ergobrush/ergobrush.github.io/img/anbo1.jpeg

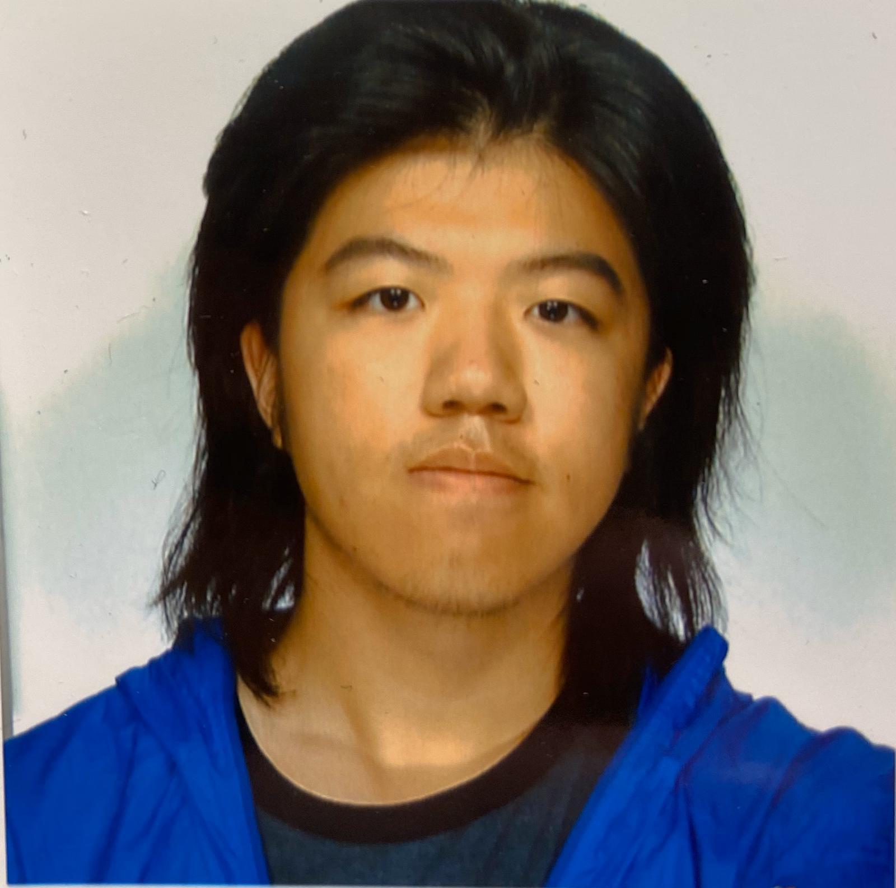
img/anbo1.jpeg
