ergobrush/ergobrush.github.io/img/andre.jpg

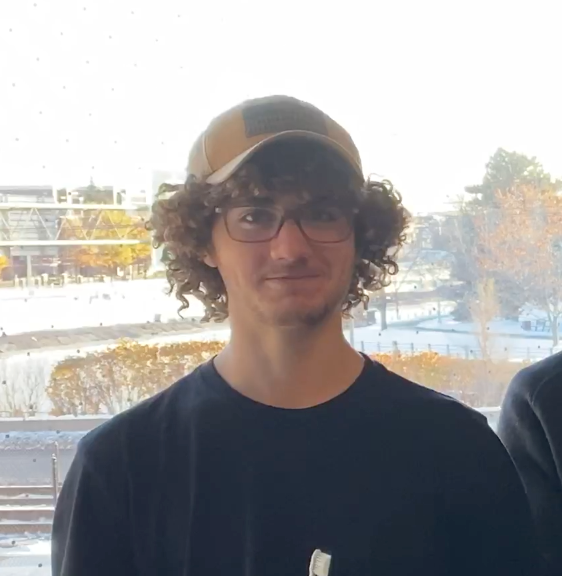
img/andre.jpg
