ergobrush/ergobrush.github.io/img/george.png

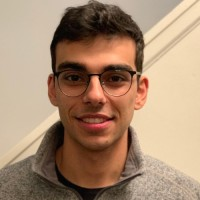
img/george.png
