ergobrush/ergobrush.github.io/img/stem-image.jpg

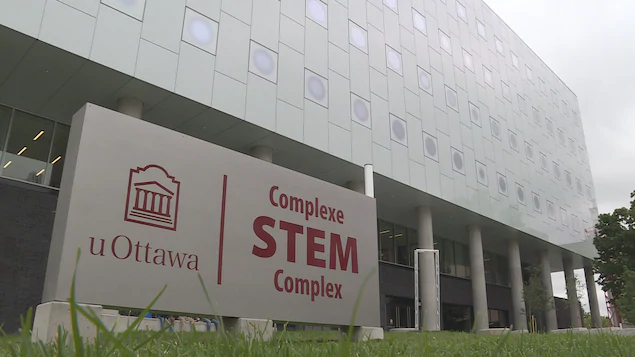
img/stem-image.jpg
