ergobrush/ergobrush.github.io/img/stvincent2.jpg

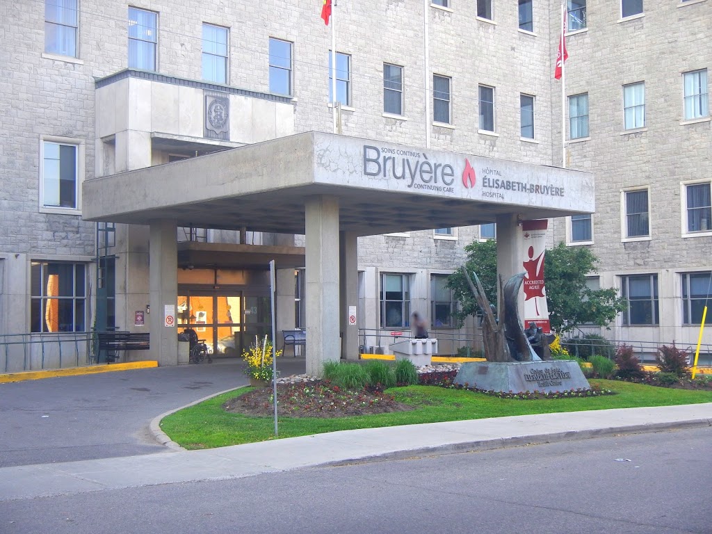
img/stvincent2.jpg
