ergobrush/ergobrush.github.io/img/toothbrush1.jpg

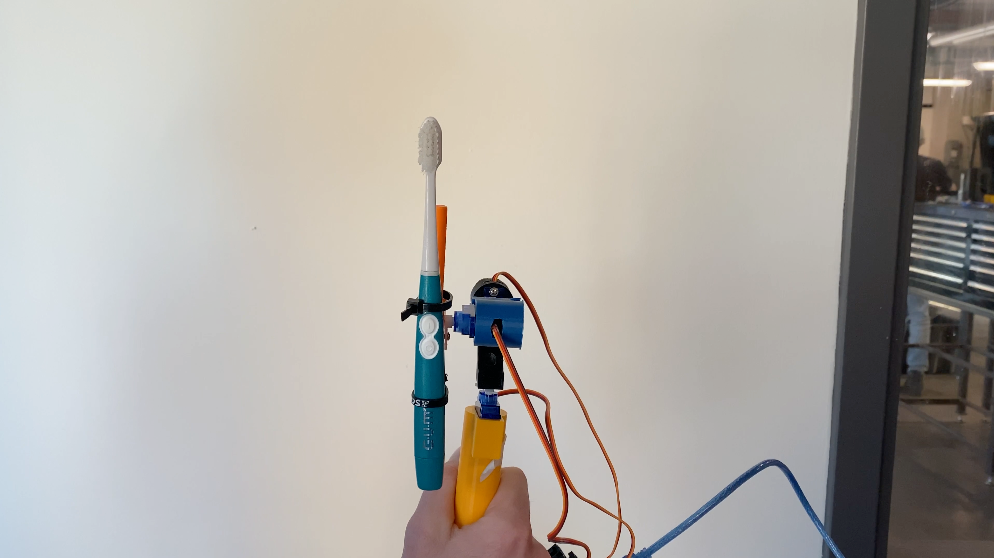
img/toothbrush1.jpg
