ergobrush/ergobrush.github.io/img/toothbrush.jpg

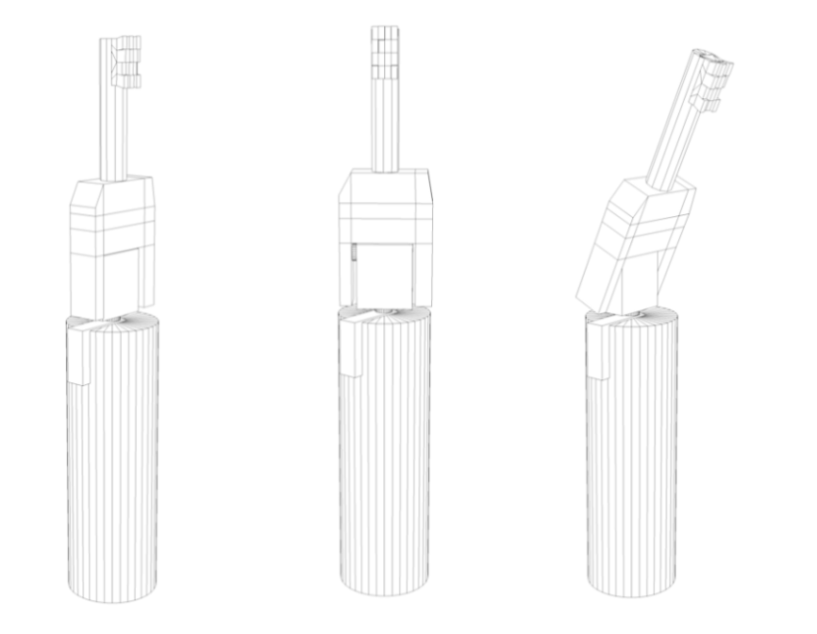
img/toothbrush.jpg
